JosselinSomervilleRoberts/LaserGame/Photos/IMG_20201130_183749.jpg

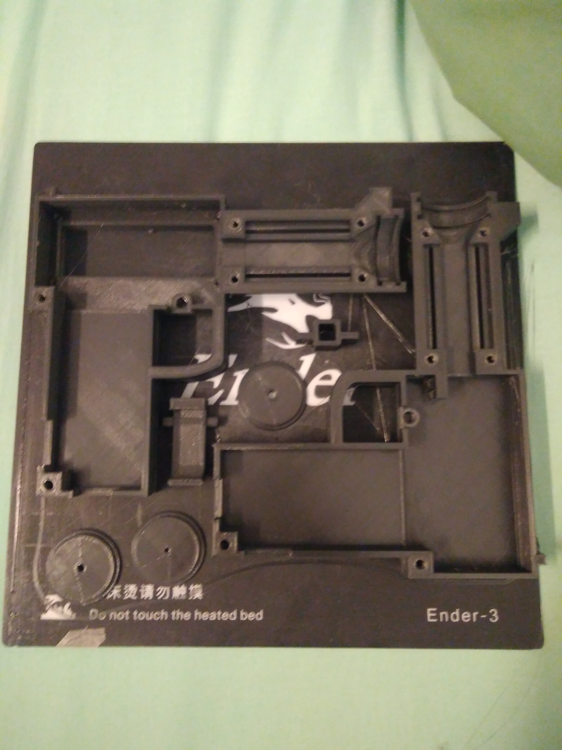
Photos/IMG_20201130_183749.jpg
