JosselinSomervilleRoberts/LaserGame/Photos/IMG_20201215_173133.jpg

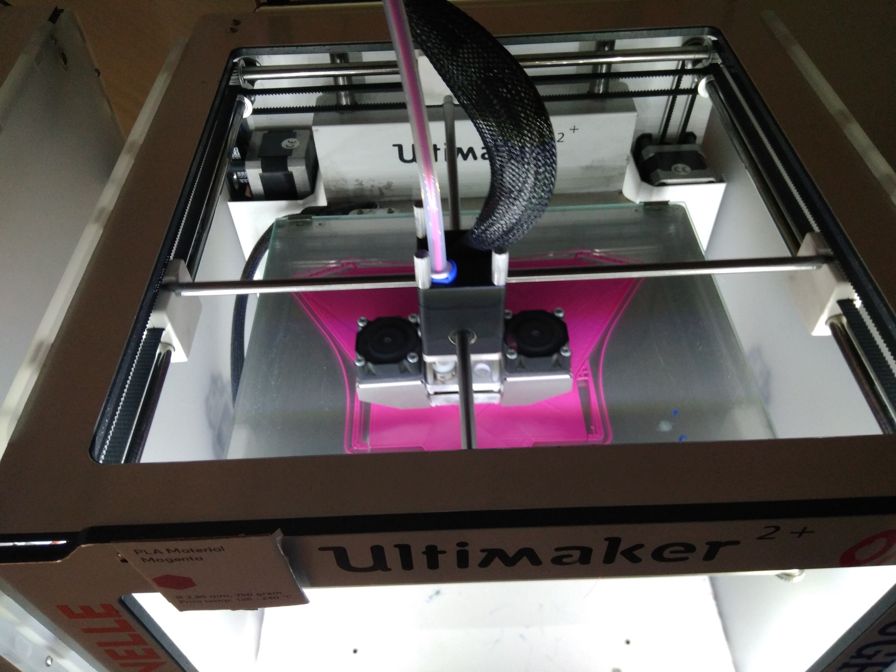
Photos/IMG_20201215_173133.jpg
