JosselinSomervilleRoberts/LaserGame/Photos/IMG_20201216_141950.jpg

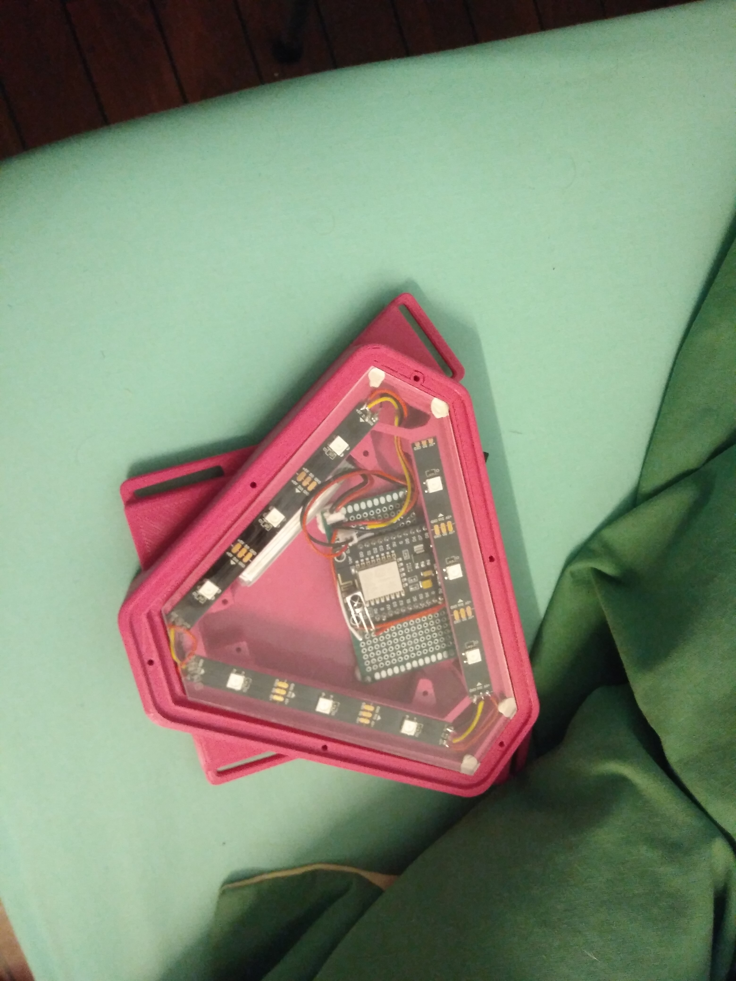
Photos/IMG_20201216_141950.jpg
