JosselinSomervilleRoberts/LaserGame/Photos/IMG_20201216_141954.jpg

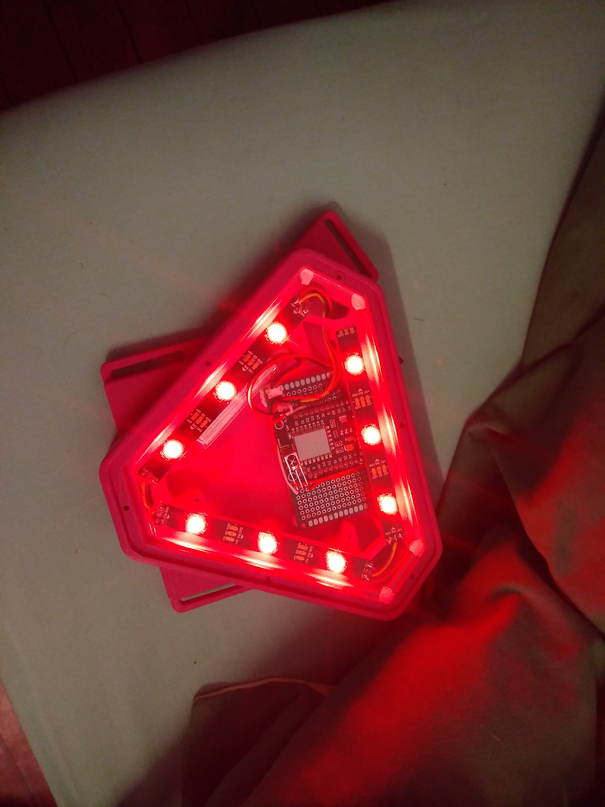
Photos/IMG_20201216_141954.jpg
