JosselinSomervilleRoberts/LaserGame/Photos/IMG_20201224_040911.jpg

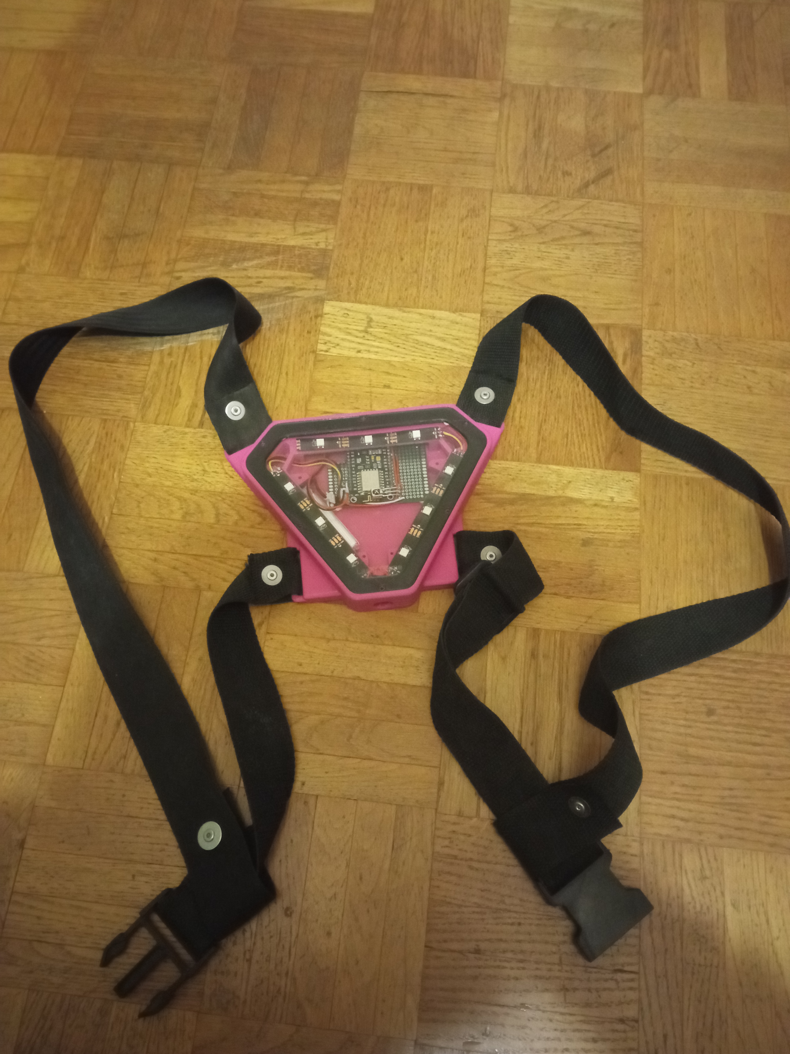
Photos/IMG_20201224_040911.jpg
