JosselinSomervilleRoberts/LaserGame/Photos/IMG_20201224_040950.jpg

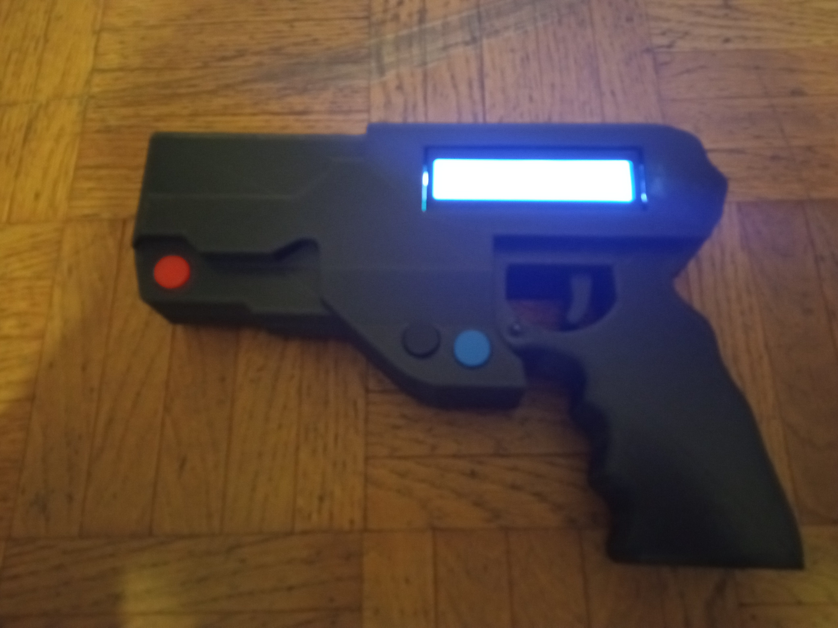
Photos/IMG_20201224_040950.jpg
