JosselinSomervilleRoberts/LaserGame/Photos/IMG_20201224_041014.jpg

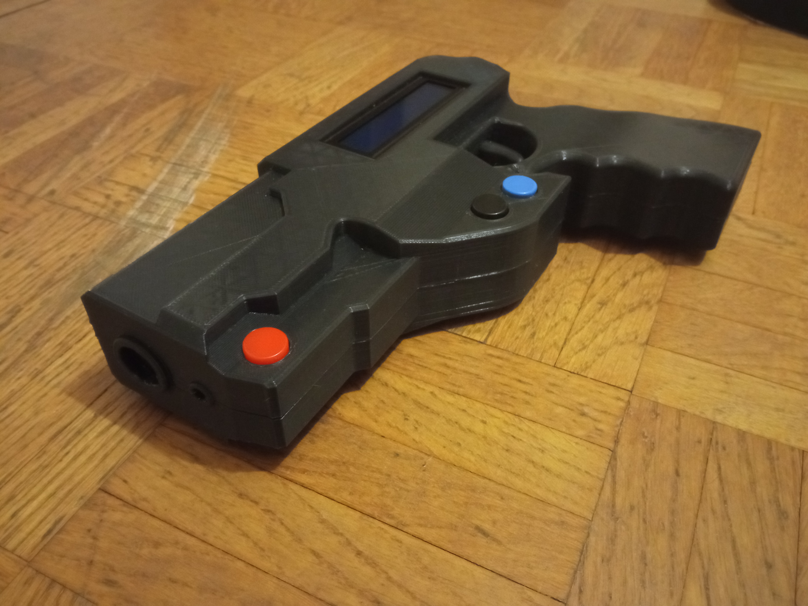
Photos/IMG_20201224_041014.jpg
