JosselinSomervilleRoberts/LaserGame/Photos/IMG_20201224_041024.jpg

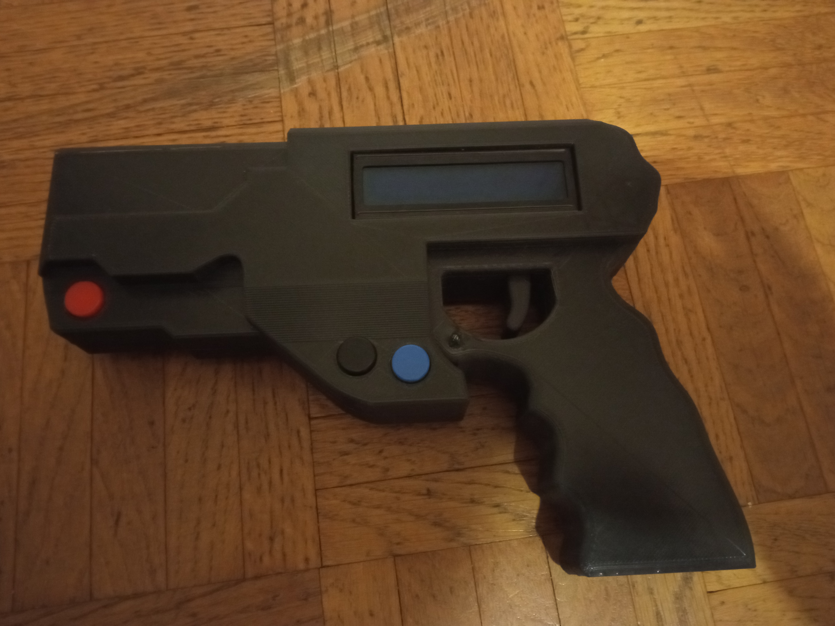
Photos/IMG_20201224_041024.jpg
