JosselinSomervilleRoberts/LaserGame/Photos/IMG_20201224_041144.jpg

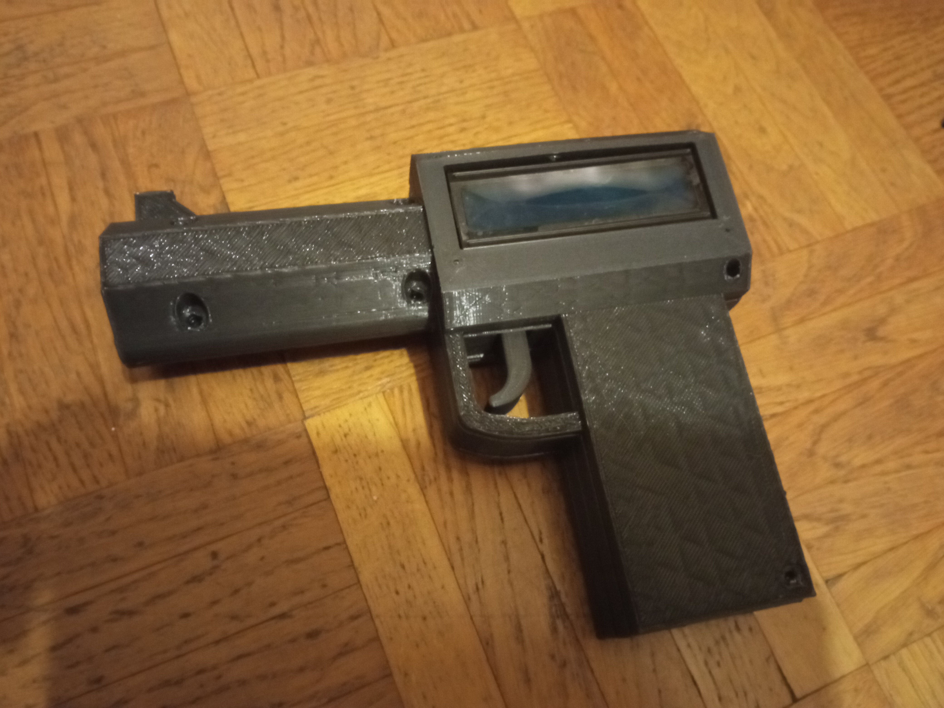
Photos/IMG_20201224_041144.jpg
