JosselinSomervilleRoberts/LaserGame/Photos/IMG_20201224_041155.jpg

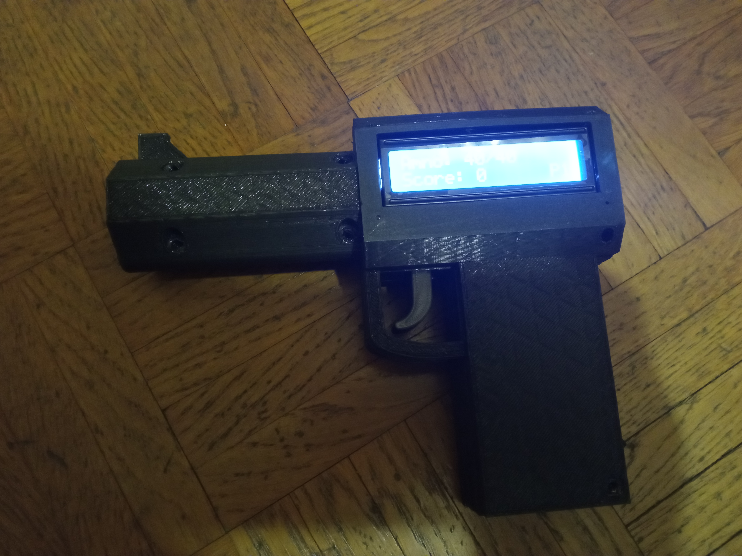
Photos/IMG_20201224_041155.jpg
