JosselinSomervilleRoberts/LaserGame/Photos/IMG_20201224_041214.jpg

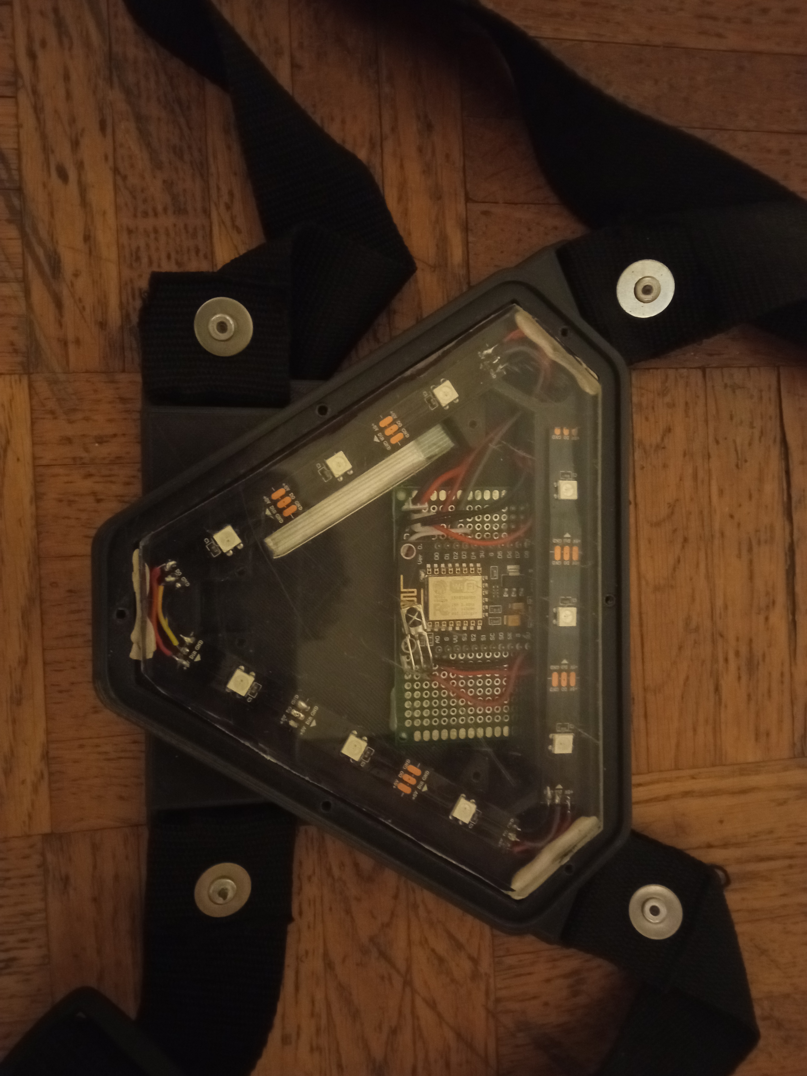
Photos/IMG_20201224_041214.jpg
