JosselinSomervilleRoberts/LaserGame/Photos/IMG_20201224_041231.jpg

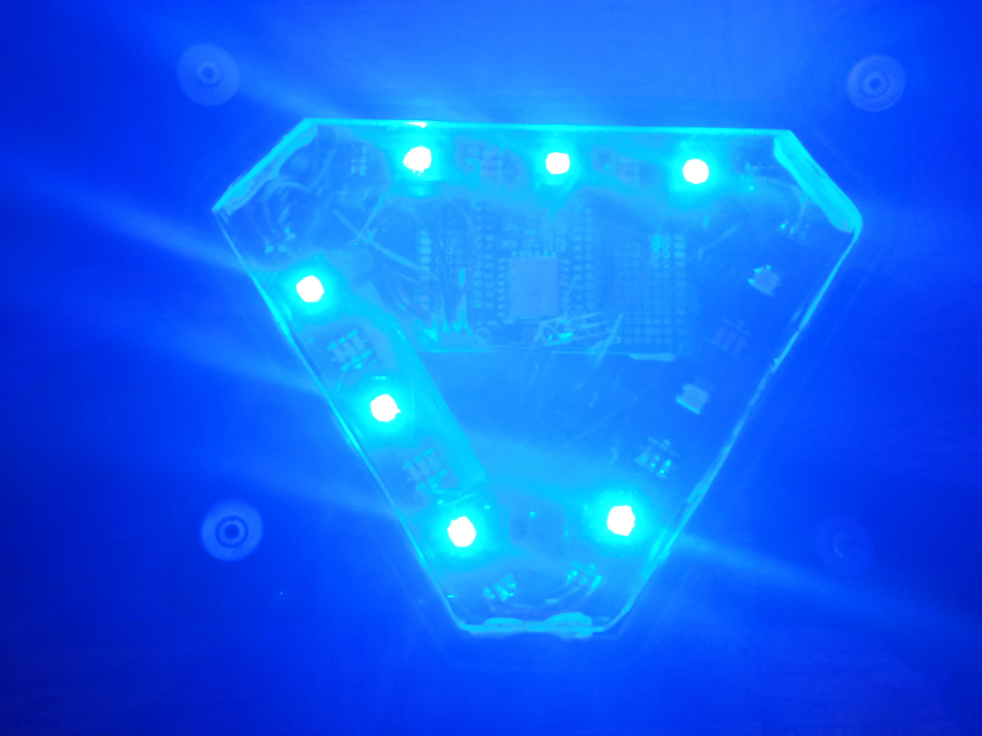
Photos/IMG_20201224_041231.jpg
