JosselinSomervilleRoberts/LaserGame/Photos/received_689087035101797.jpeg

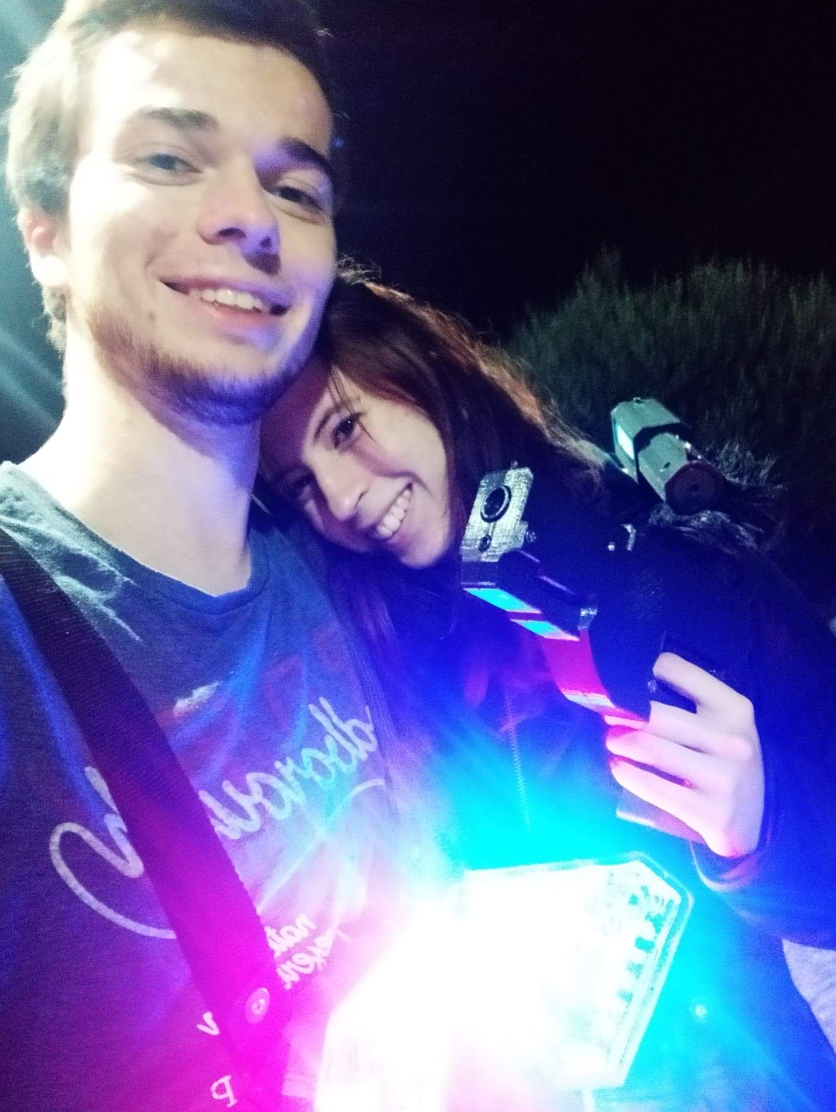
Photos/received_689087035101797.jpeg
