JosselinSomervilleRoberts/LaserGame/SolidWorks/chargeur.JPG

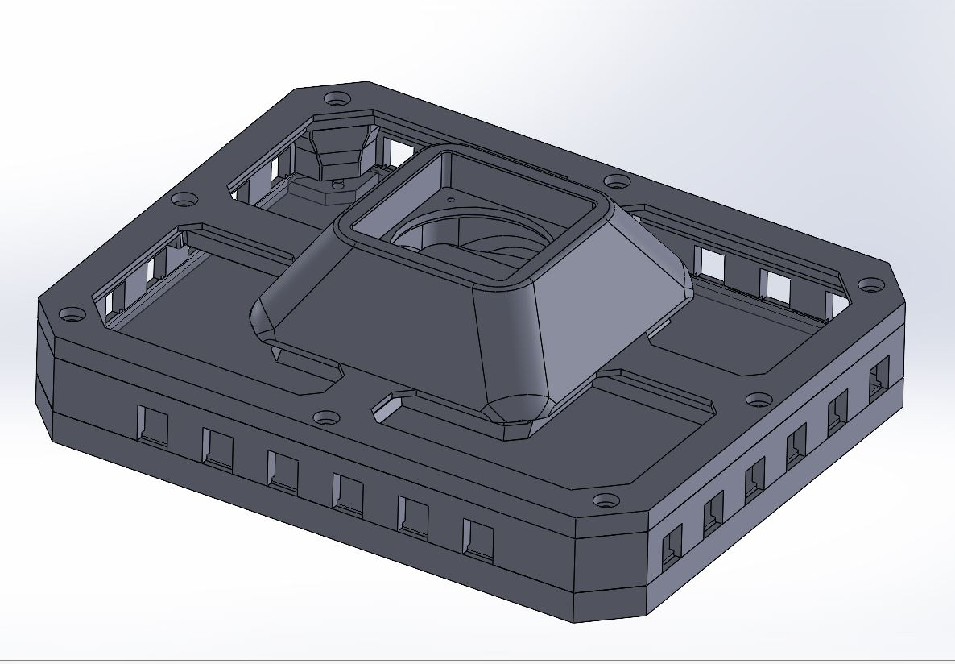
SolidWorks/chargeur.JPG
