JosselinSomervilleRoberts/LaserGame/SolidWorks/pistolet.JPG

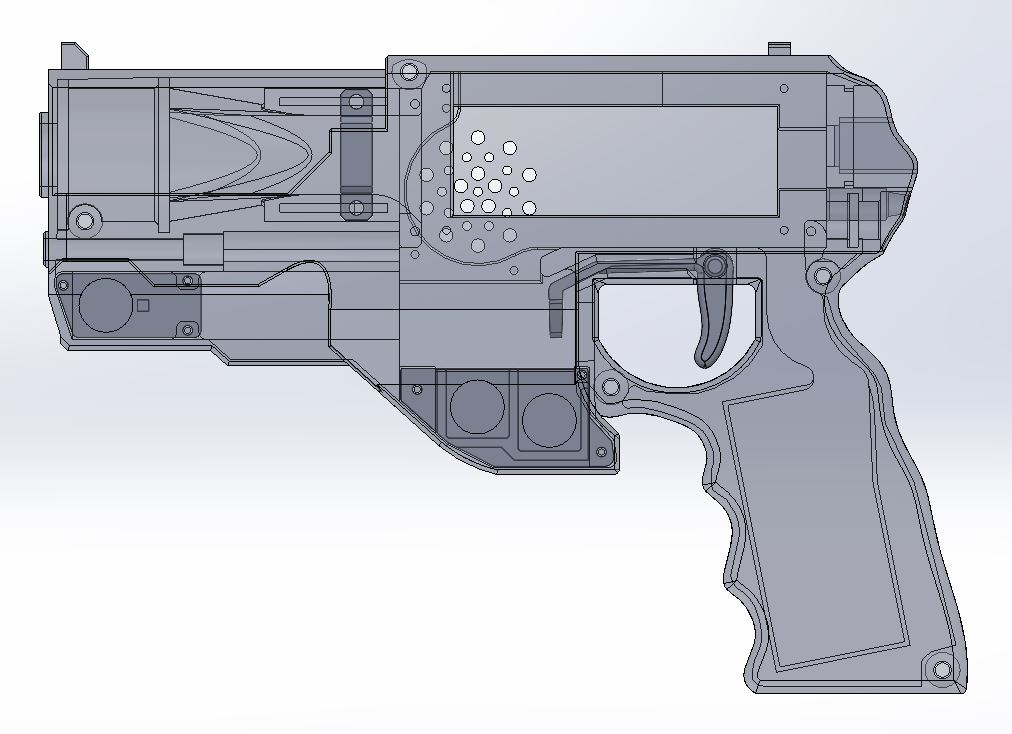
SolidWorks/pistolet.JPG
