JosselinSomervilleRoberts/LaserGame/SolidWorks/plastron.JPG

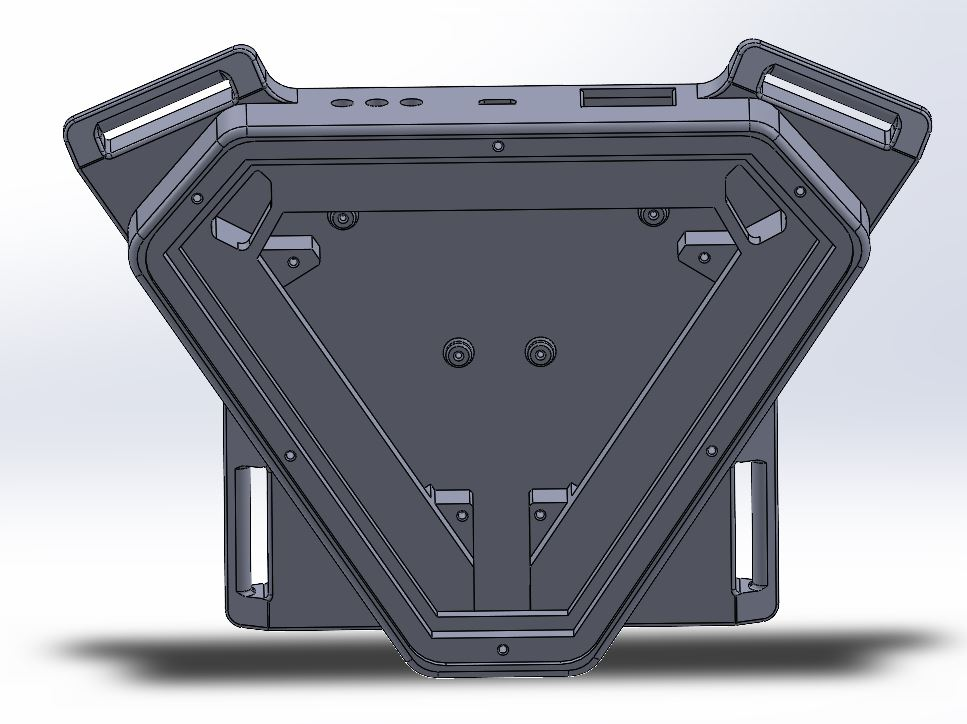
SolidWorks/plastron.JPG
