JosselinSomervilleRoberts/LaserGame/SolidWorks/plastron v1/plastron_avant.SLDPRT

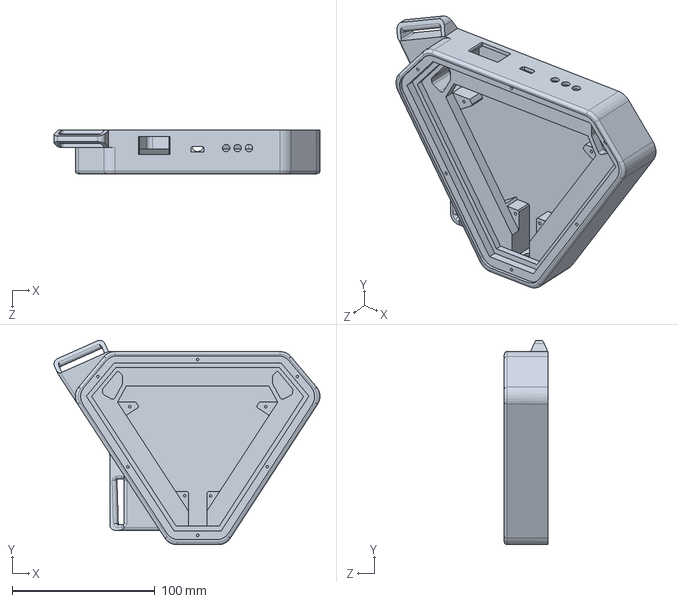
[picture p39: CAD file, 2021-06-21]
SolidWorks/plastron v1/plastron_avant.SLDPRT
186.5 x 143.2 x 30.5 mm
