JosselinSomervilleRoberts/LaserGame/SolidWorks/pistolet v3/gachette_v4.STL

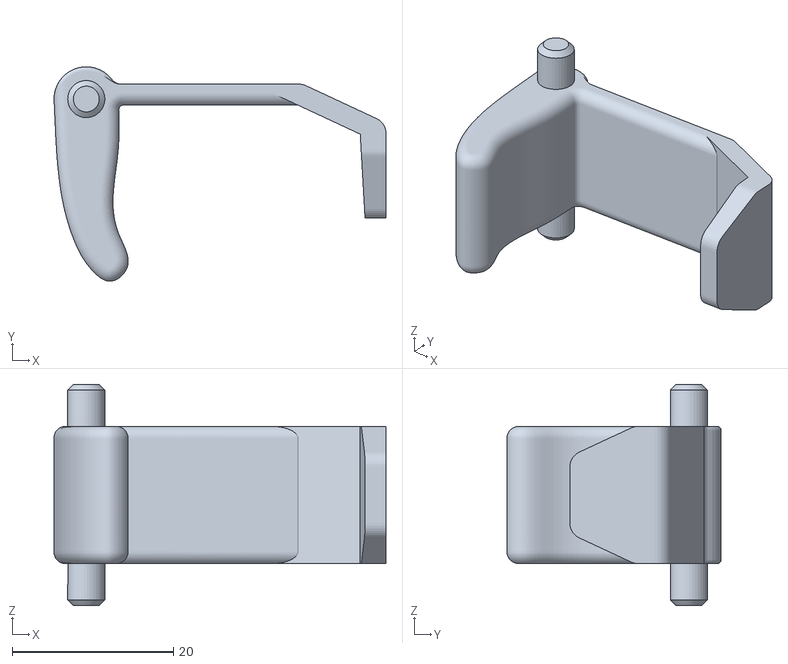
[picture p40: CAD file, 2021-06-21]
SolidWorks/pistolet v3/gachette_v4.STL
41.1 x 26.6 x 27.4
