JosselinSomervilleRoberts/LaserGame/SolidWorks/plastron v1/plastron_avant_12_01.STL

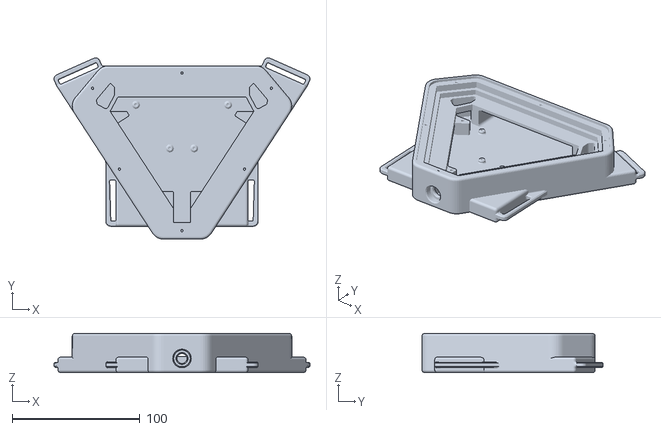
[picture p41: CAD file, 2021-06-21]
SolidWorks/plastron v1/plastron_avant_12_01.STL
200.1 x 141.6 x 30.5
