JosselinSomervilleRoberts/LaserGame/SolidWorks/chargeur v1/piece_milieu.SLDPRT

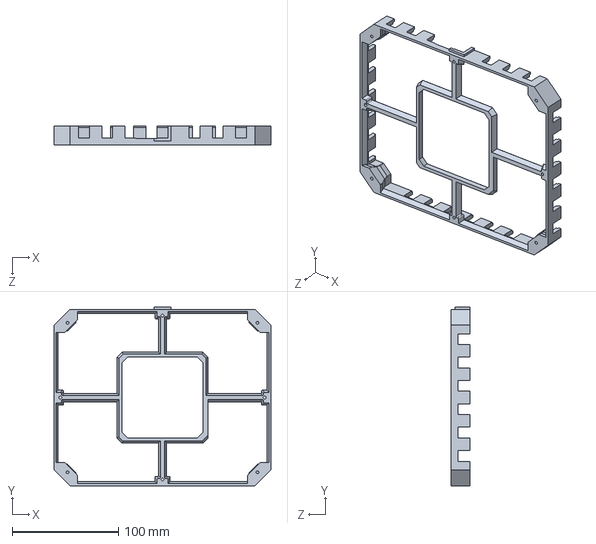
[picture p42: CAD file, 2021-06-21]
SolidWorks/chargeur v1/piece_milieu.SLDPRT
204.5 x 168.4 x 18.0 mm
