JosselinSomervilleRoberts/LaserGame/SolidWorks/pistolet v3/19_01_pistolet_cote_rien.STL

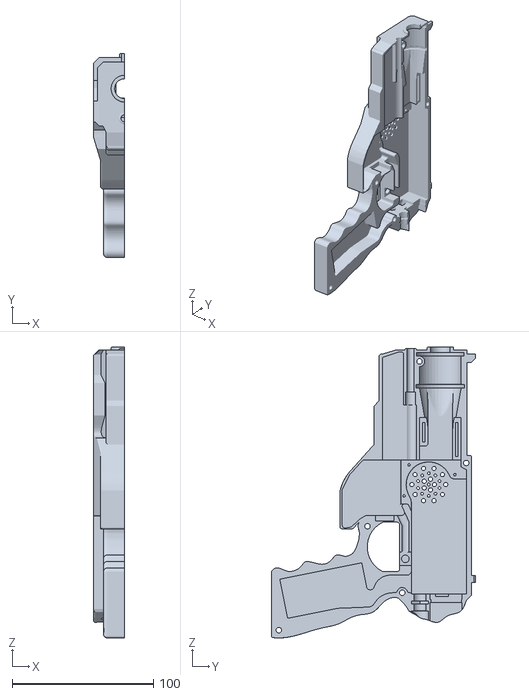
[picture p43: CAD file, 2021-06-21]
SolidWorks/pistolet v3/19_01_pistolet_cote_rien.STL
22.0 x 144.7 x 206.3
