JosselinSomervilleRoberts/LaserGame/SolidWorks/plastron v1/plexiglass.SLDPRT

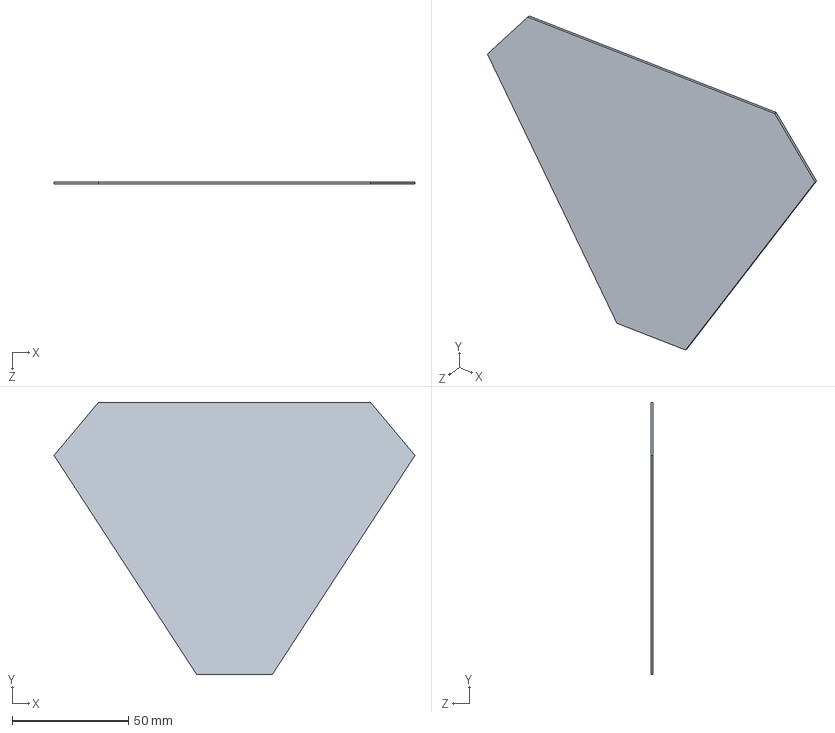
[picture p44: CAD file, 2021-06-21]
SolidWorks/plastron v1/plexiglass.SLDPRT
155.3 x 117.1 x 1.00 mm
