JosselinSomervilleRoberts/LaserGame/SolidWorks/chargeur v1/couvercle.SLDPRT

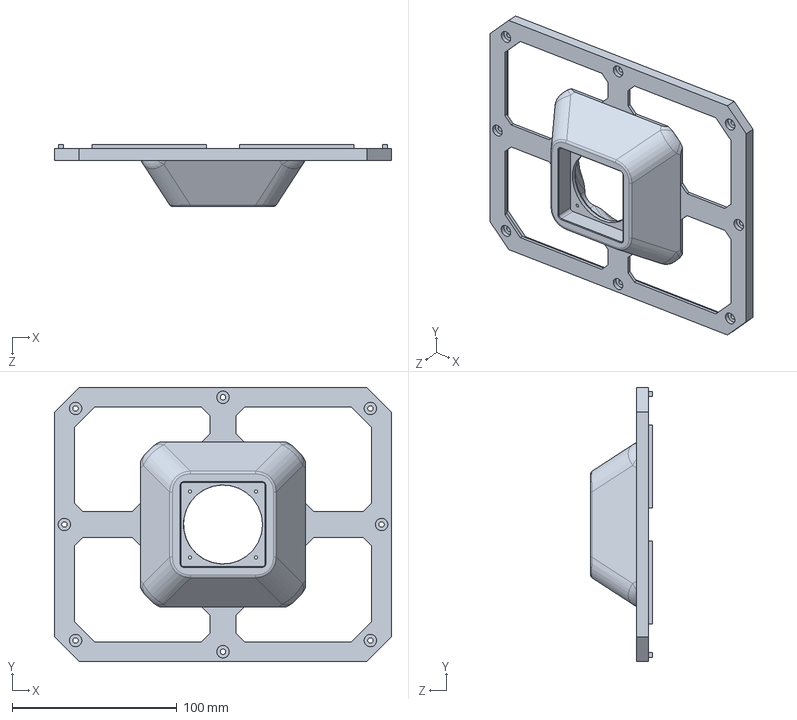
[picture p45: CAD file, 2021-06-21]
SolidWorks/chargeur v1/couvercle.SLDPRT
204.5 x 166.4 x 37.5 mm
