JosselinSomervilleRoberts/LaserGame/SolidWorks/plastron v1/Pièce3.SLDPRT

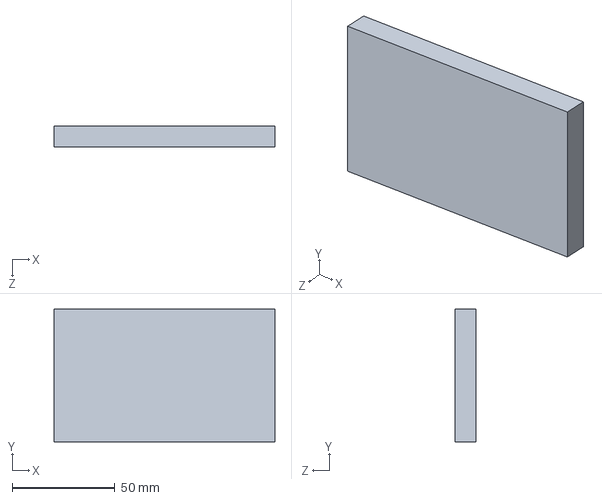
[picture p46: CAD file, 2021-06-21]
SolidWorks/plastron v1/Pièce3.SLDPRT
107.5 x 64.5 x 10.0 mm
