JosselinSomervilleRoberts/LaserGame/SolidWorks/pistolet v3/diaphragme_6.SLDPRT

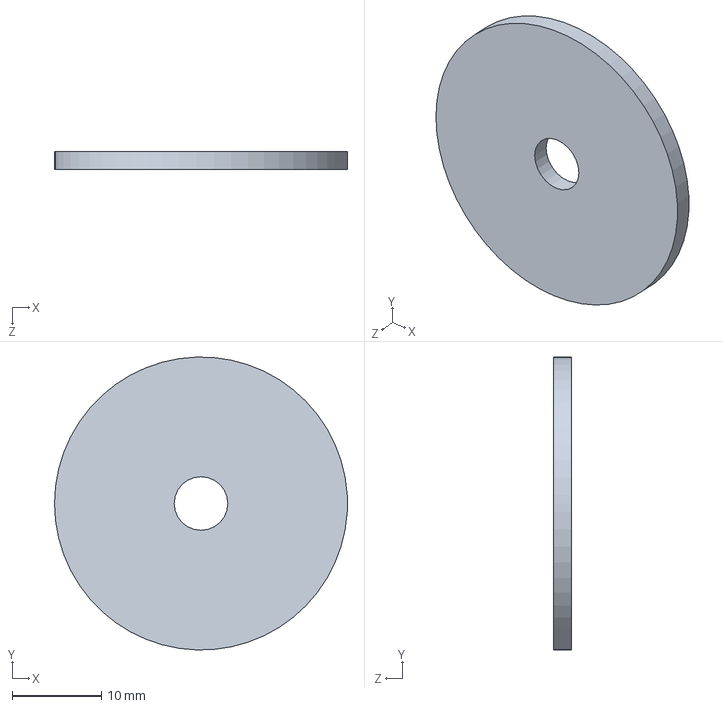
[picture p47: CAD file, 2021-06-21]
SolidWorks/pistolet v3/diaphragme_6.SLDPRT
32.8 x 32.8 x 2.00 mm
