JosselinSomervilleRoberts/LaserGame/SolidWorks/plastron v1/plastron_avant_new2.SLDPRT

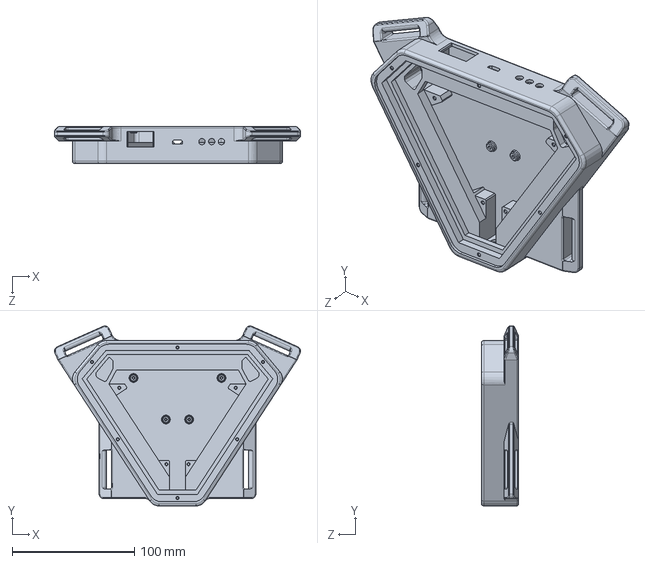
[picture p48: CAD file, 2021-06-21]
SolidWorks/plastron v1/plastron_avant_new2.SLDPRT
201.4 x 147.3 x 30.5 mm
