JosselinSomervilleRoberts/LaserGame/SolidWorks/pistolet v3/coulisseau_v3.SLDPRT

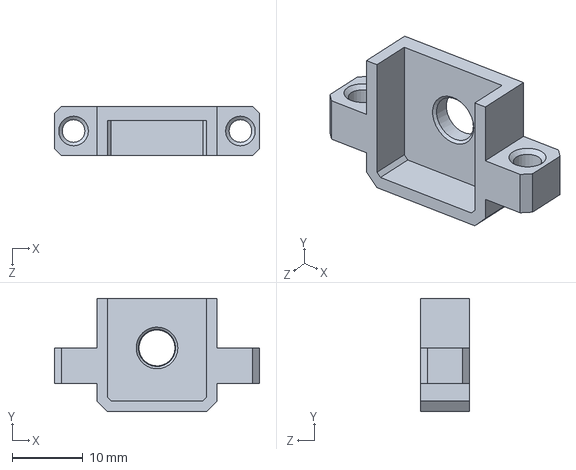
[picture p49: CAD file, 2021-06-21]
SolidWorks/pistolet v3/coulisseau_v3.SLDPRT
29.0 x 16.0 x 7.00 mm
