JosselinSomervilleRoberts/LaserGame/SolidWorks/plastron v1/cache_batterie.SLDPRT

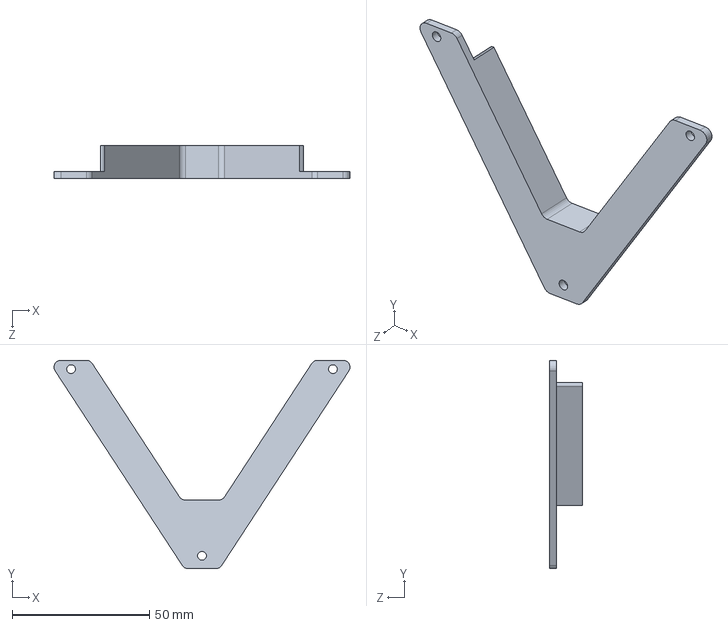
[picture p50: CAD file, 2021-06-21]
SolidWorks/plastron v1/cache_batterie.SLDPRT
107.7 x 75.9 x 12.0 mm
