JosselinSomervilleRoberts/LaserGame/SolidWorks/pistolet v3/pistolet_cote_circuit.SLDPRT

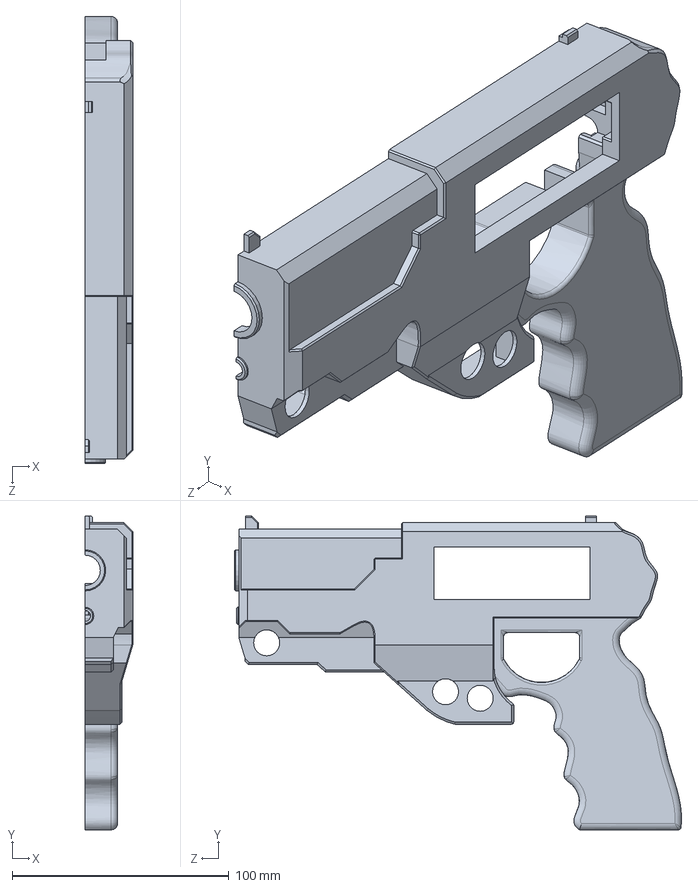
[picture p51: CAD file, 2021-06-21]
SolidWorks/pistolet v3/pistolet_cote_circuit.SLDPRT
22.0 x 144.7 x 206.3 mm
