JosselinSomervilleRoberts/LaserGame/SolidWorks/pistolet v3/plaque_interrupteur_canon.SLDPRT

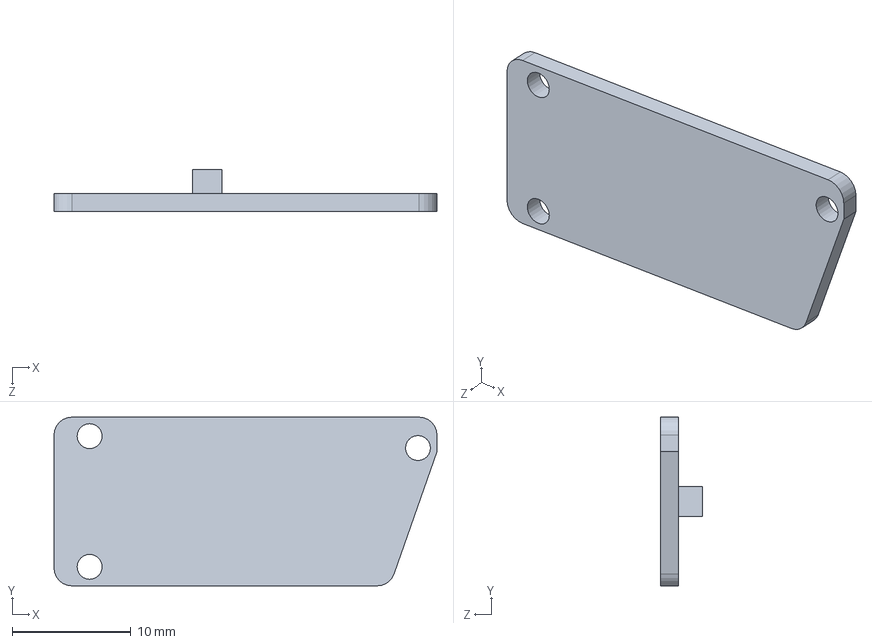
[picture p52: CAD file, 2021-06-21]
SolidWorks/pistolet v3/plaque_interrupteur_canon.SLDPRT
32.2 x 14.2 x 3.50 mm
