JosselinSomervilleRoberts/LaserGame/SolidWorks/pistolet v3/Pistoler_entier.SLDPRT

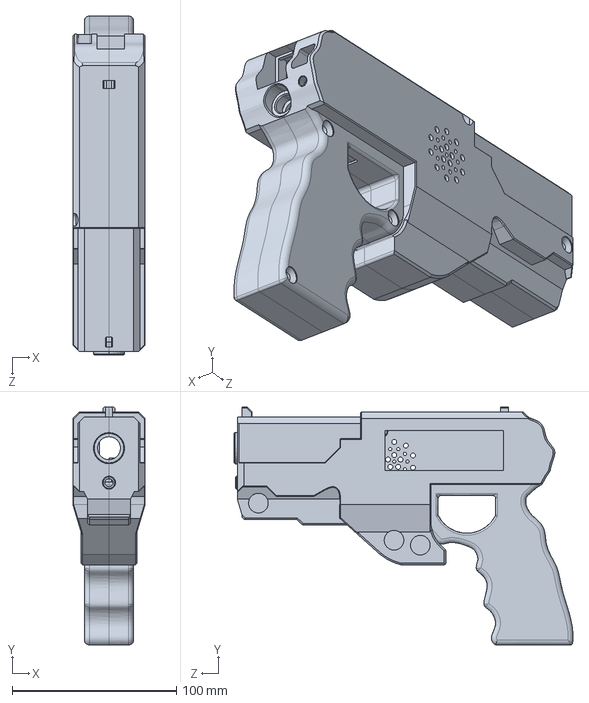
[picture p53: CAD file, 2021-06-21]
SolidWorks/pistolet v3/Pistoler_entier.SLDPRT
44.0 x 144.7 x 206.3 mm
