JosselinSomervilleRoberts/LaserGame/SolidWorks/plastron v1/pcb_plastron_v1.SLDPRT

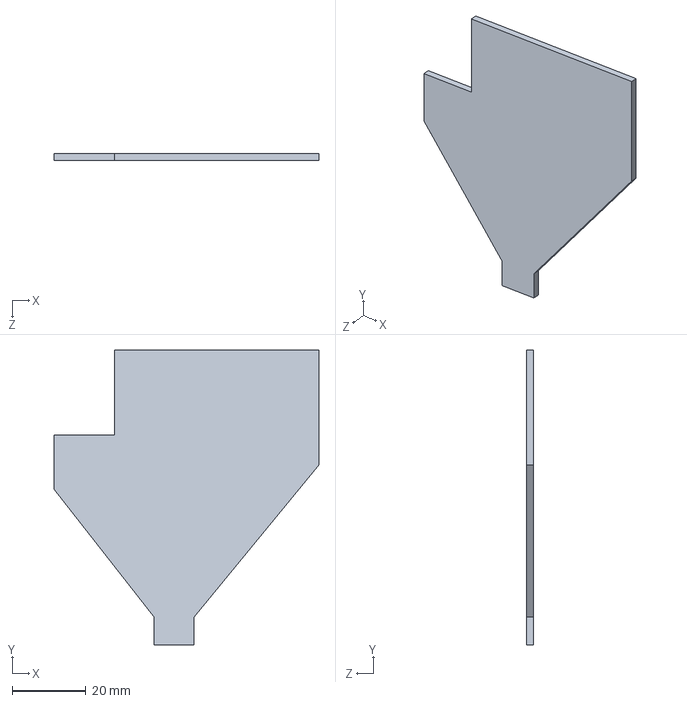
[picture p54: CAD file, 2021-06-21]
SolidWorks/plastron v1/pcb_plastron_v1.SLDPRT
71.8 x 80.0 x 2.00 mm
