JosselinSomervilleRoberts/LaserGame/SolidWorks/plastron v1/plastron_avant_11_01.STL

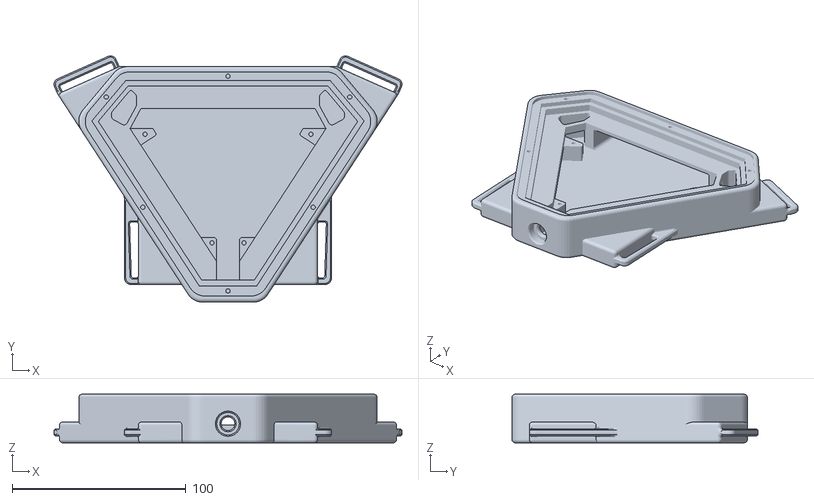
[picture p55: CAD file, 2021-06-21]
SolidWorks/plastron v1/plastron_avant_11_01.STL
200.1 x 141.6 x 28.0
