JosselinSomervilleRoberts/LaserGame/SolidWorks/pistolet v3/diaphragme_6_v5.SLDPRT

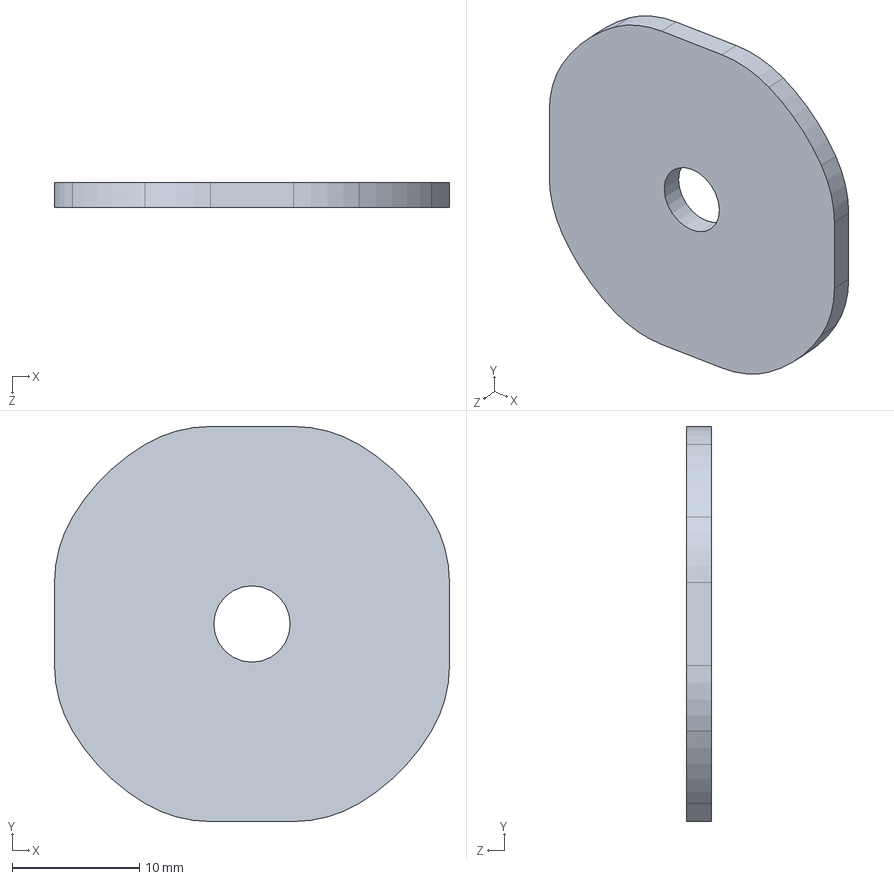
[picture p56: CAD file, 2021-06-21]
SolidWorks/pistolet v3/diaphragme_6_v5.SLDPRT
31.0 x 31.0 x 2.00 mm
