JosselinSomervilleRoberts/LaserGame/SolidWorks/pistolet v3/plaque_interrupteur_crosse.SLDPRT

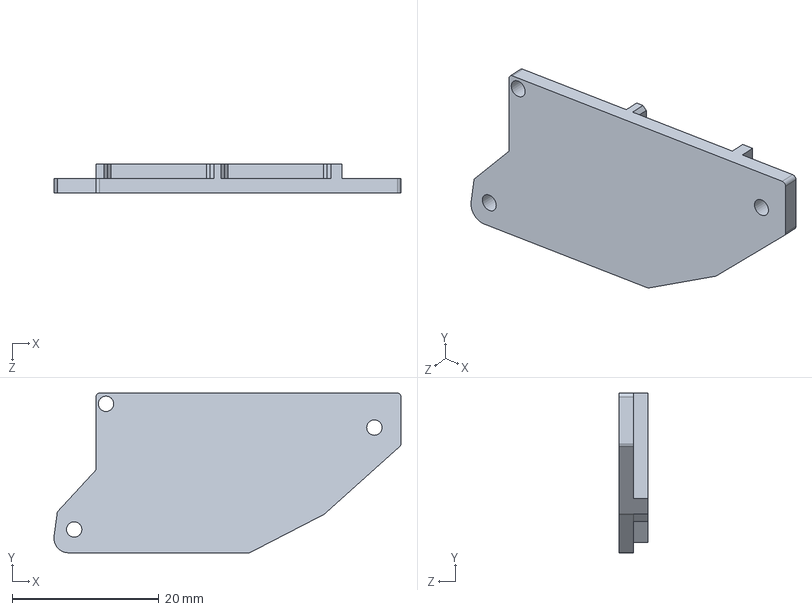
[picture p57: CAD file, 2021-06-21]
SolidWorks/pistolet v3/plaque_interrupteur_crosse.SLDPRT
47.3 x 21.8 x 4.00 mm
